jkleiber/quadrotor/software/control_sim/src/control_sim_gui.cpp

#include "control_sim/control_sim_gui.h"

bool GuiManager::InitGui()
{
    if (SDL_Init(SDL_INIT_VIDEO | SDL_INIT_TIMER | SDL_INIT_GAMECONTROLLER) !=
        0)
    {
        printf("Error: %s\n", SDL_GetError());
        return false;
    }

    // Decide GL+GLSL versions
#if defined(IMGUI_IMPL_OPENGL_ES2)
    // GL ES 2.0 + GLSL 100
    const char *glsl_version = "#version 100";
    SDL_GL_SetAttribute(SDL_GL_CONTEXT_FLAGS, 0);
    SDL_GL_SetAttribute(SDL_GL_CONTEXT_PROFILE_MASK, SDL_GL_CONTEXT_PROFILE_ES);
    SDL_GL_SetAttribute(SDL_GL_CONTEXT_MAJOR_VERSION, 2);
    SDL_GL_SetAttribute(SDL_GL_CONTEXT_MINOR_VERSION, 0);
#elif defined(__APPLE__)
    // GL 3.2 Core + GLSL 150
    const char *glsl_version = "#version 150";
    SDL_GL_SetAttribute(
        SDL_GL_CONTEXT_FLAGS,
        SDL_GL_CONTEXT_FORWARD_COMPATIBLE_FLAG); // Always required on Mac
    SDL_GL_SetAttribute(SDL_GL_CONTEXT_PROFILE_MASK,
                        SDL_GL_CONTEXT_PROFILE_CORE);
    SDL_GL_SetAttribute(SDL_GL_CONTEXT_MAJOR_VERSION, 3);
    SDL_GL_SetAttribute(SDL_GL_CONTEXT_MINOR_VERSION, 2);
#else
    // GL 3.0 + GLSL 130
    const char *glsl_version = "#version 130";
    SDL_GL_SetAttribute(SDL_GL_CONTEXT_FLAGS, 0);
    SDL_GL_SetAttribute(SDL_GL_CONTEXT_PROFILE_MASK,
                        SDL_GL_CONTEXT_PROFILE_CORE);
    SDL_GL_SetAttribute(SDL_GL_CONTEXT_MAJOR_VERSION, 3);
    SDL_GL_SetAttribute(SDL_GL_CONTEXT_MINOR_VERSION, 0);
#endif

    // Create window with graphics context
    SDL_GL_SetAttribute(SDL_GL_DOUBLEBUFFER, 1);
    SDL_GL_SetAttribute(SDL_GL_DEPTH_SIZE, 24);
    SDL_GL_SetAttribute(SDL_GL_STENCIL_SIZE, 8);
    SDL_WindowFlags window_flags = (SDL_WindowFlags)(
        SDL_WINDOW_OPENGL | SDL_WINDOW_RESIZABLE | SDL_WINDOW_ALLOW_HIGHDPI);
    window = SDL_CreateWindow("Control Simulation", SDL_WINDOWPOS_CENTERED,
                              SDL_WINDOWPOS_CENTERED, 1280, 720, window_flags);
    gl_context = SDL_GL_CreateContext(window);
    SDL_GL_MakeCurrent(window, gl_context);
    SDL_GL_SetSwapInterval(1); // Enable vsync

    // Setup Dear ImGui context
    IMGUI_CHECKVERSION();
    ImGui::CreateContext();

    // Setup Dear ImGui style
    ImGui::StyleColorsDark();
    // ImGui::StyleColorsClassic();

    // Setup Platform/Renderer backends
    ImGui_ImplSDL2_InitForOpenGL(window, gl_context);
    ImGui_ImplOpenGL3_Init(glsl_version);

    // Setup ImPlot context
    ImPlot::CreateContext();

    return true;
}

bool GuiManager::UpdateGui()
{
    // Get I/O
    ImGuiIO &io = ImGui::GetIO();

    // Process SDL events.
    SDL_Event event;
    while (SDL_PollEvent(&event))
    {
        ImGui_ImplSDL2_ProcessEvent(&event);
        if (event.type == SDL_QUIT)
            return false;
        if (event.type == SDL_WINDOWEVENT &&
            event.window.event == SDL_WINDOWEVENT_CLOSE &&
            event.window.windowID == SDL_GetWindowID(window))
            return false;
    }

    // Start the Dear ImGui frame
    ImGui_ImplOpenGL3_NewFrame();
    ImGui_ImplSDL2_NewFrame();
    ImGui::NewFrame();

    bool sim_control_active = false;
    ImGui::Begin("Simulation Control", &sim_control_active);
    gui_events_->start_sim = ImGui::Button("Start");
    gui_events_->stop_sim = ImGui::Button("Stop");
    gui_events_->reset_sim = ImGui::Button("Reset");
    ImGui::End();

    // ImPlot::ShowDemoWindow();

    return true;
}

bool GuiManager::Render()
{
    // Get I/O
    ImGuiIO &io = ImGui::GetIO();

    // Clear color
    ImVec4 clear_color = ImVec4(0.45f, 0.55f, 0.60f, 1.00f);

    // Rendering
    ImGui::Render();
    glViewport(0, 0, (int)io.DisplaySize.x, (int)io.DisplaySize.y);
    glClearColor(clear_color.x * clear_color.w, clear_color.y * clear_color.w,
                 clear_color.z * clear_color.w, clear_color.w);
    glClear(GL_COLOR_BUFFER_BIT);
    ImGui_ImplOpenGL3_RenderDrawData(ImGui::GetDrawData());
    SDL_GL_SwapWindow(window);

    return true;
}

bool GuiManager::CloseGui()
{
    // Cleanup
    ImGui_ImplOpenGL3_Shutdown();
    ImGui_ImplSDL2_Shutdown();
    ImGui::DestroyContext();

    SDL_GL_DeleteContext(gl_context);
    SDL_DestroyWindow(window);
    SDL_Quit();

    return true;
}
