jkleiber/quadrotor/software/control_sim/include/control_sim/pid_controller.h

#ifndef PIDCONTROLLER_H
#define PIDCONTROLLER_H

// TODO: move completely away from RobotLib implementation
#include "RobotLibUtil.h"
#include <chrono>
#include <algorithm>
#include <math.h>

#include "control_sim/sim_clock.h"


class PIDController
{
    public:
        // Constructors
        PIDController(SimClock *clk) : clk_(clk)
        {
            this->Init();
            this->Start(0.0);
        }

        PIDController(SimClock *clk, float init_state, float kp, float ki, float kd) : clk_(clk)
        {
            this->Init();
            this->Start(init_state, kp, ki, kd);
        }

        // Copy assignment
        void operator=(const PIDController& pid);

        // Init
        void Init();

        // Setters
        void Start(float init_state);
        void Start(float init_state, float kp, float ki, float kd);
        void Reset();
        void SetBounded(bool bounded);
        void SetOutputRange(float lower, float upper);
        void SetTolerance(float setpoint_tol, float derivative_tol, bool apply_tolerance);
        void SetIntegratorBounds(float min, float max);

        // Getters
        float Update(float tarGetState, float cur_state);
        float GetIntegratorValue();

    private:
        // PID values
        float derivative;
        float integrator;
        float error;

        // States
        float prev_error;
        float last_state;

        // Equation coefficients
        float kP;
        float kI;
        float kD;

        // Boundary control
        float high;
        float low;
        bool is_bounded;

        // Timing
        SimClock const* clk_;
        double last_time;
        float dt;

        // Tolerance control
        float setpoint_tolerance;
        float derivative_tolerance;
        bool tolerance_enabled;

        // Integrator controls
        float integrator_min;
        float integrator_max;
};

#endif // PIDCONTROLLER_H
